ShaneWhitmore/TechnologyAndTheBody/CAD Files/Prototype/right Palm.3mf

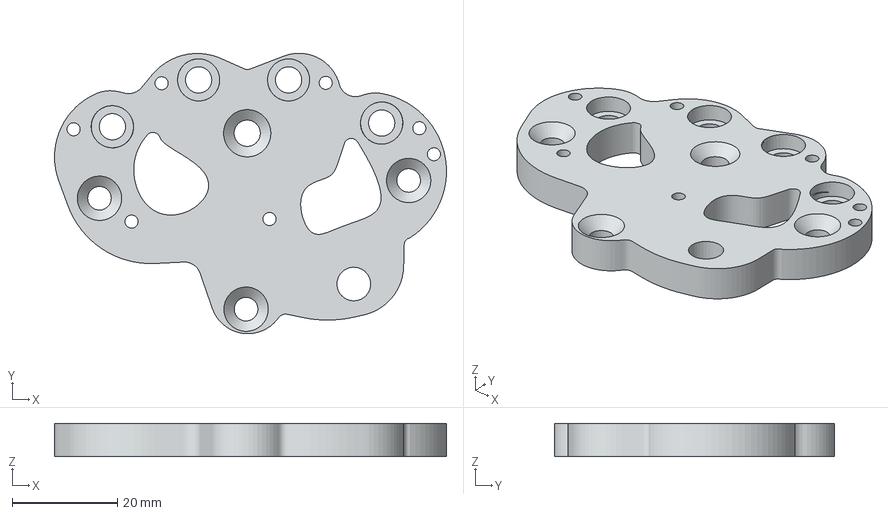
[picture p97: CAD file, 2025-09-30]
CAD Files/Prototype/right Palm.3mf
74.5 x 53.3 x 6.35 mm
